zshni/8-Ifargan-St.-door-lock/Ifargan door lock with PIR.sch

## EAGLE design Ifargan door lock with PIR.sch (2016-01-01)

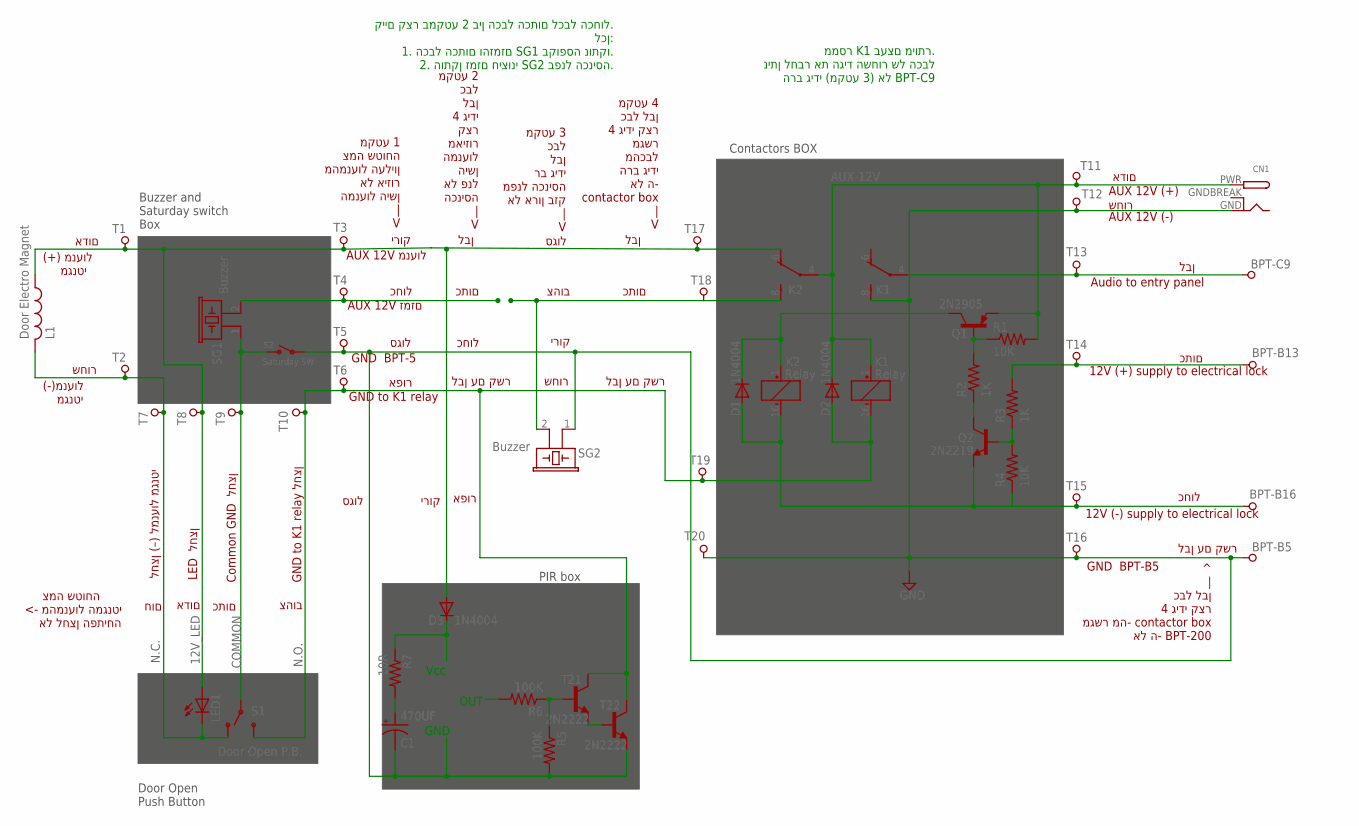
[picture p3: schematic Ifargan door lock with PIR.sch]

Parts:
BPT-B5, BPT-B13, BPT-B16: PAD_TERMINAL-4.1MMROUND; PAD_ROUND_4.1MM
BPT-C9: PAD_TERMINAL-4.1MMROUND; PAD_ROUND_4.1MM
C1: 470UF; EIA3216
CN1: DCBARRELPTH; DCJACK_2MM_PTH
D1, D2, D3: 1N4004; DO41-10
K1, K2: Relay; DS2Y
L1: Door Electro Magnet; IRF-3
LED1: LED; SMARTLED-TTW
Q1: 2N2905; TO5
Q2: 2N2219; TO5
R1, R4: 10K; 0207/15
R2, R3: 1K; 0207/15
R5, R6: 100K; 0207/15
R7: 10R; 0207/15
S1: Door Open P.B.; KPS-1290
S2: Saturday SW; SPST_SMT_19192
SG1, SG2: Buzzer; F/EE21P
T1, T2, T3, T4, T5, T6, T7, T8, T9, T10, T11, T12, T13, T14, T15, T16, T17, T18, T19, T20: PAD_TERMINAL-4.1MMROUND; PAD_ROUND_4.1MM
T21, T22: 2N2222; TO92-EBC-OVAL

Connections:
12V_LED: K2.6 (O), L1.1, LED1.A@1 (A), T1.P, T3.P, T8.P, T17.P
AUX-12V: CN1.PWR, D2.C, K1.1 (+), K2.4, Q1.1 (E), R1.2, T11.P
COMMON: S1.P, S2.C (S), SG1.1, T9.P
GND: BPT-B5.P, C1.C (-), CN1.GND, K1.8 (S), R5.2, S2.B, SG2.1, T5.P, T12.P, T16.P, T20.P, T22.E
unnamed: Q2.2 (B), R3.1, R4.2
unnamed: Q1.2 (B), R1.1, R2.2
unnamed: SG1.2, T4.P
unnamed: BPT-B16.P, D1.A, K2.16 (-), Q2.1 (E), R4.1, T15.P
unnamed: Q2.3 (C), R2.1
unnamed: BPT-B13.P, R3.2, T14.P
unnamed: BPT-C9.P, K1.4
unnamed: K2.8 (S), SG2.2, T18.P
unnamed: D1.C, K2.1 (+), Q1.3 (C)
unnamed: D3.C, R7.1
unnamed: T21.E, T22.B
unnamed: R5.1, R6.1, T21.B
unnamed: C1.A (+), R7.2
N.C.: L1.2, LED1.C@1 (C), S1.O, T2.P, T7.P
N.O.: D2.A, K1.16 (-), S1.S, T6.P, T10.P, T19.P, T21.C, T22.C

Notes on the sheet:
Door Open Push Button
Buzzer and Saturday switch Box
Contactors BOX
(+) מנעול מגנטי
(-)מנעול מגנטי
AUX 12V מנעול
AUX 12V זמזם
GND BPT-5
GND to K1 relay
לחצן (–) למנעול מגנטי
LED לחצן
Common GND לחצן
GND to K1 relay לחצן
AUX 12V (+)
AUX 12V (-)
12V (+) supply to electrical lock
12V (-) supply to electrical lock
Audio to entry panel
GND BPT-B5
חום
אדום
כתום
צהוב
צמה שטוחה <- מהמנעול המגנטי אל לחצן הפתיחה
מקטע 1 צמה שטוחה מהמנעול העליון אל איזור המנעול הישן | V
ירוק
כחול
סגול
אפור
לבן
לבן עם קשר
שחור
מקטע 2 כבל לבן 4 גידי קצר מאיזור המנעול הישן אל פנל הכניסה | V
מקטע 3 כבל לבן רב גידי מפנל הכניסה אל ארון בזק | V
מקטע 4 כבל לבן 4 גידי קצר מגשר מהכבל הרב גידי אל ה- contactor box | V
^ | כבל לבן 4 גידי קצר מגשר מה- contactor box אל ה- BPT-200
קיים קצר במקטע 2 בין הכבל הכתום לכבל הכחול. לכן: 1. הכבל הכתום והזמזם SG1 בקופסה נותקו. 2. הותקן זמזם חיצוני SG2 בפנל הכניסה.
ממסר K1 בעצם מיותר. ניתן לחבר את הגיד השחור של הכבל הרב גידי (מקטע 3) אל BPT-C9
PIR Sensor
PIR box
Vcc
GND
OUT
