zshni/8-Ifargan-St.-door-lock/buzzer 12v limiter.sch

## EAGLE design buzzer 12v limiter.sch (2016-01-03)

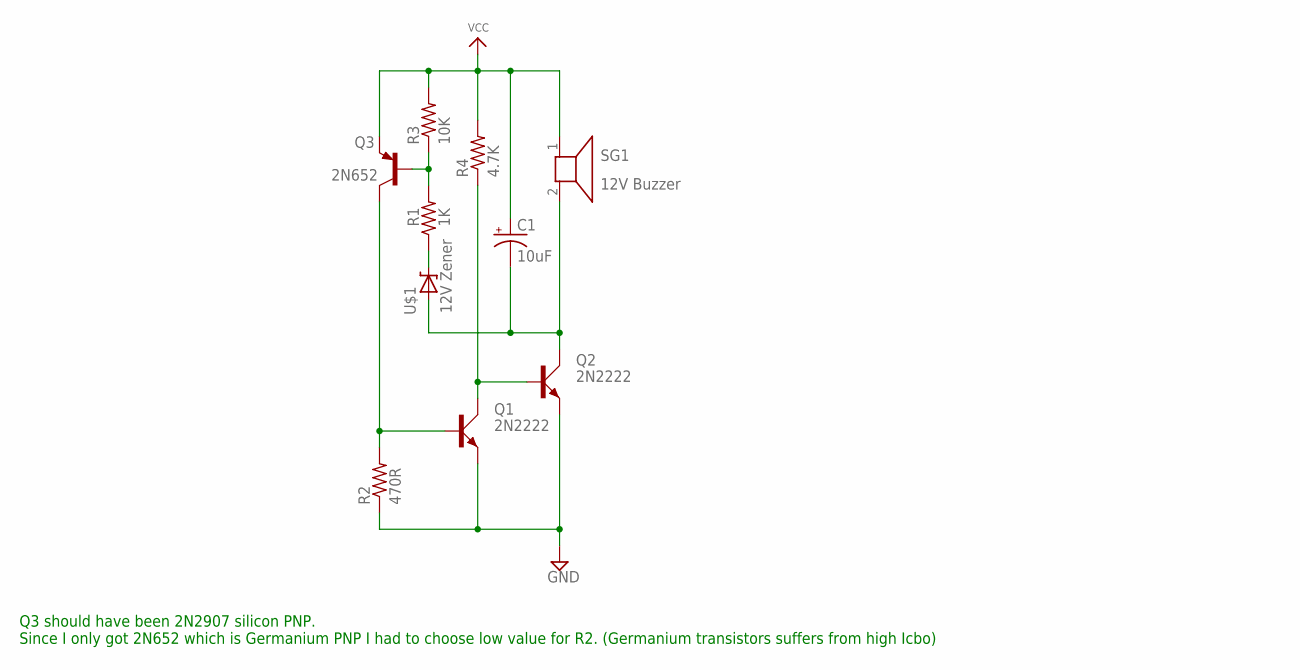
[picture p4: schematic buzzer 12v limiter.sch]

Parts:
C1: 10uF; PANASONIC_H13
Q1, Q2: 2N2222; TO18A
Q3: 2N652; TO18
R1: 1K; 0805-THM
R2: 470R; 0805-THM
R3: 10K; 0805-THM
R4: 4.7K; 0805-THM
SG1: 12V Buzzer; F/SMX
U$1: 12V Zener; DIODE-ZENER

Connections:
GND: Q1.E, Q2.E, R2.1
unnamed: Q1.C, Q2.B, R4.1
unnamed: C1.-, Q2.C, SG1.2, U$1.P$2 (A)
unnamed: Q3.2 (B), R1.2, R3.1
unnamed: R1.1, U$1.P$1 (C)
unnamed: Q1.B, Q3.3 (C), R2.2
VCC: C1.+, Q3.1 (E), R3.2, R4.2, SG1.1

Notes on the sheet:
Q3 should have been 2N2907 silicon PNP. Since I only got 2N652 which is Germanium PNP I had to choose low value for R2. (Germanium transistors suffers from high Icbo)
